Maobuff/MaoRad/doc/pictures/signal4.BMP

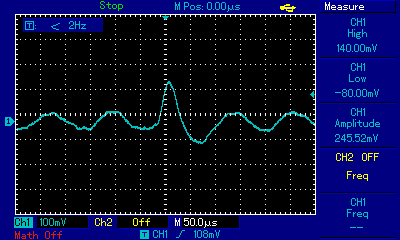
doc/pictures/signal4.BMP
