Maobuff/MaoRad/doc/pictures/signal5.BMP

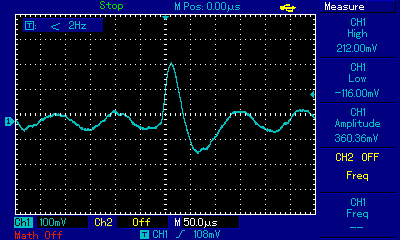
doc/pictures/signal5.BMP
